Vishnuvardhanchowhan/RFID-Attendance-system-design/MON-08_Code/EDL_MFRC_REGISTER/myLib.h

/*
 * myLib.h
 *
 *  Created on: 09-Feb-2023
 *      Author: Aksh garg
 */

#ifndef MYLIB_H_
#define MYLIB_H_

#include<math.h>
#include <stdint.h>
#include <stdbool.h>
#include <string.h>
#include "inc/hw_types.h"
#include "inc/hw_memmap.h"
#include "driverlib/sysctl.h"
#include "driverlib/gpio.h"
#include "inc/hw_ints.h"
#include "driverlib/interrupt.h"
#include "driverlib/timer.h"
#include <time.h>
#include "driverlib/adc.h"
#include "driverlib/ssi.h"
#include "inc/hw_ssi.h"
#include "driverlib/pin_map.h"

#endif /* MYLIB_H_ */
